MisterHW/EVAL-MP8862/doc/ev8862_image.jpg

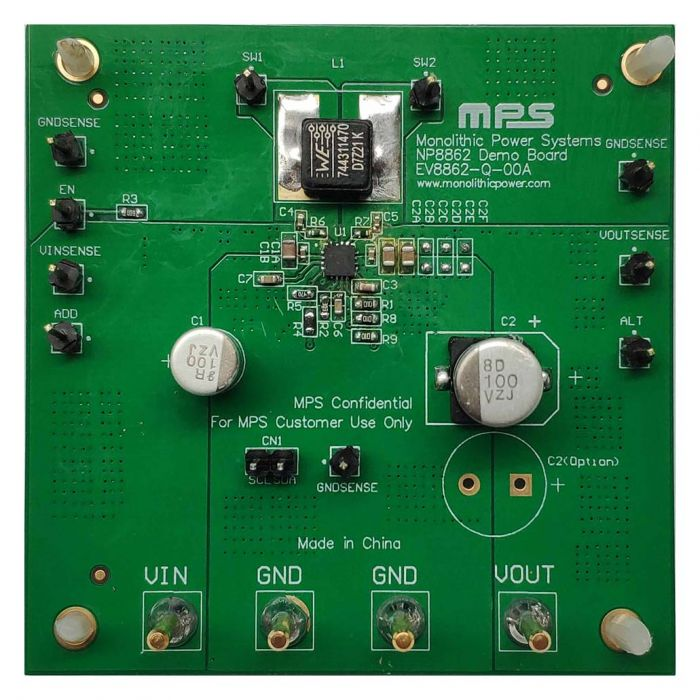
doc/ev8862_image.jpg
