MisterHW/EVAL-MP8862/img/read_0x00_0xFF_uart_starts_out_of_order_STM32F7_potential_problem.PNG

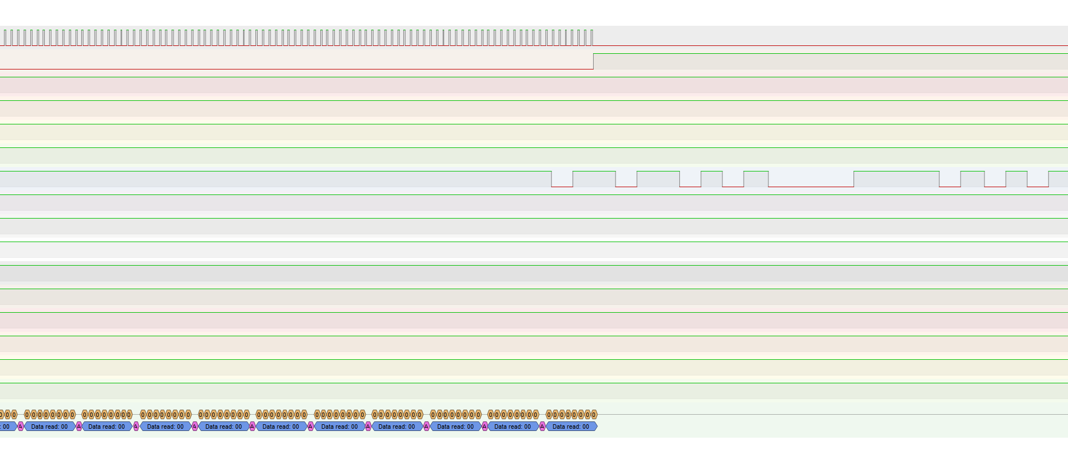
img/read_0x00_0xFF_uart_starts_out_of_order_STM32F7_potential_problem.PNG
