MisterHW/EVAL-MP8862/EVAL-MP8862-1A/gerber/EVAL-MP8862-In1_Cu.pdf

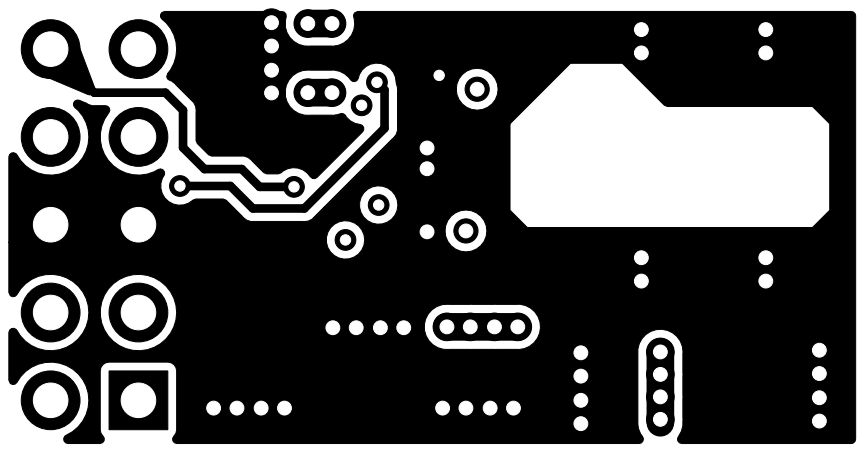
[picture p60: page 1]

File: EVAL-MP8862.kicad_pcb Sheet: https://github.com/MisterHW
