MisterHW/EVAL-MP8862/EVAL-MP8862-1A/gerber/EVAL-MP8862-In2_Cu.pdf

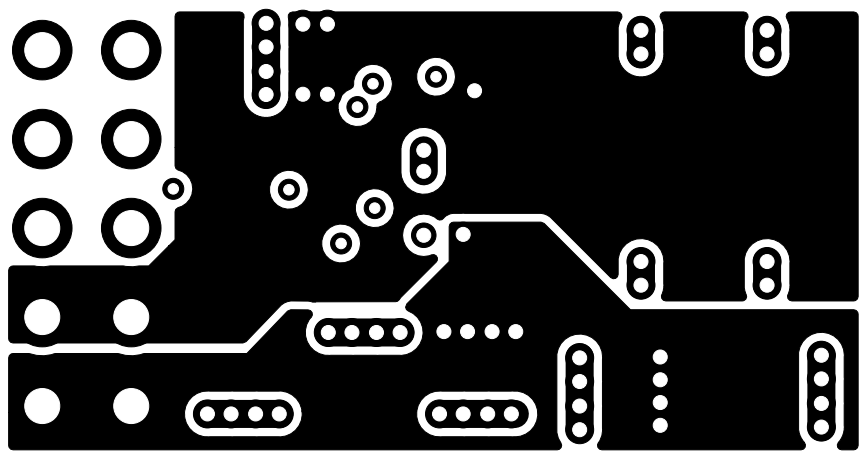
[picture p61: page 1]

File: EVAL-MP8862.kicad_pcb Sheet: https://github.com/MisterHW
