MisterHW/EVAL-MP8862/EVAL-MP8862-1B/gerber/EVAL-MP8862-B_Cu.pdf

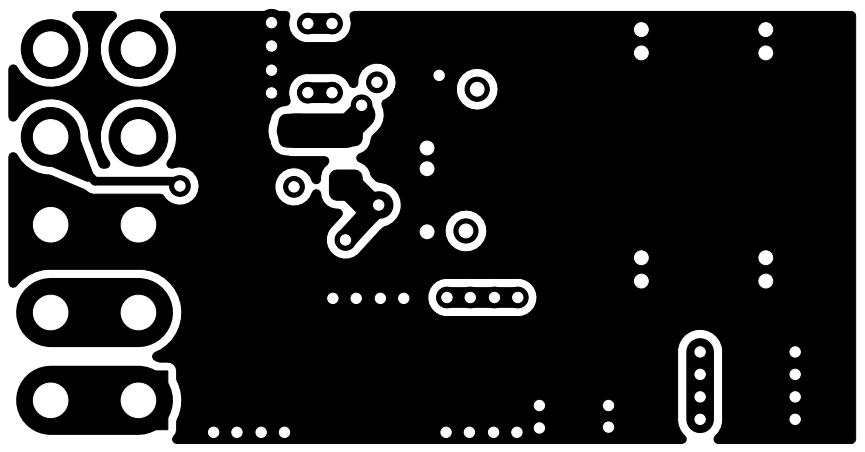
[picture p63: page 1]

File: EVAL-MP8862.kicad_pcb Sheet: https://github.com/MisterHW
