MisterHW/EVAL-MP8862/EVAL-MP8862-1B/gerber/EVAL-MP8862-B_Paste.pdf

File: EVAL-MP8862.kicad_pcb Sheet: https://github.com/MisterHW
