MisterHW/EVAL-MP8862/EVAL-MP8862-1B/gerber/EVAL-MP8862-F_Paste.pdf

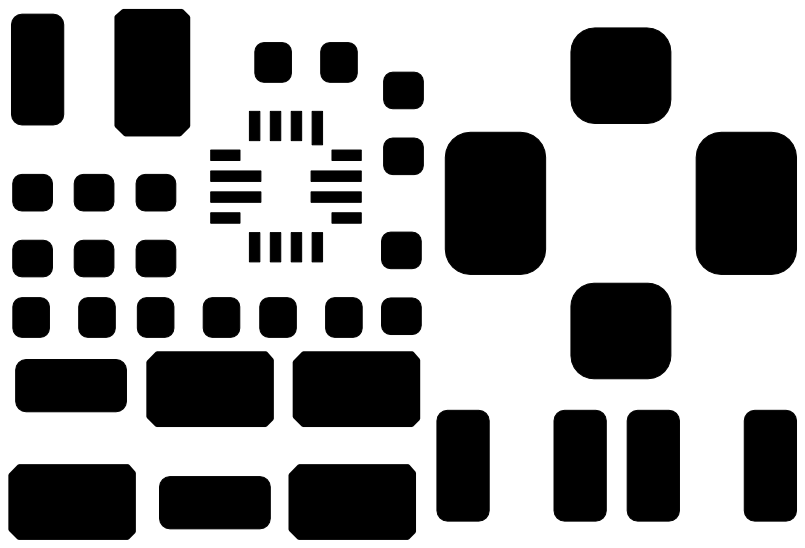
[picture p66: page 1]

File: EVAL-MP8862.kicad_pcb Sheet: https://github.com/MisterHW
