MisterHW/EVAL-MP8862/EVAL-MP8862-1B/gerber/EVAL-MP8862-In2_Cu.pdf

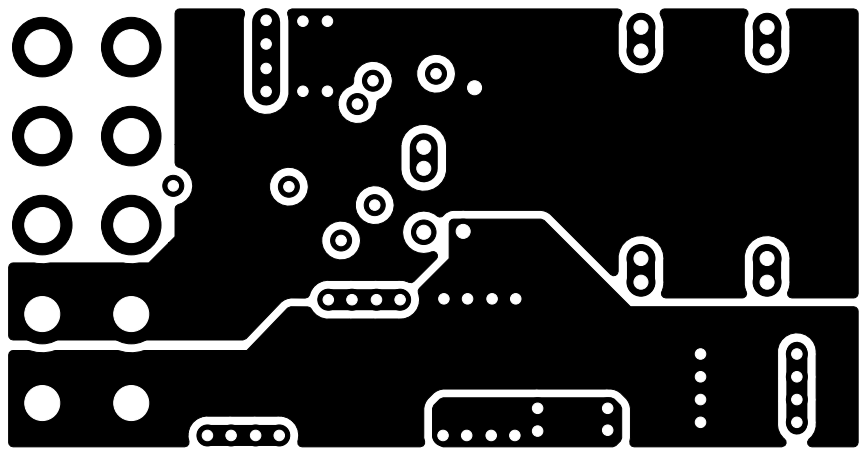
[picture p68: page 1]

File: EVAL-MP8862.kicad_pcb Sheet: https://github.com/MisterHW
