MisterHW/EVAL-MP8862/EVAL-MP8862-1B/gerber/EVAL-MP8862-B_Silkscreen.pdf

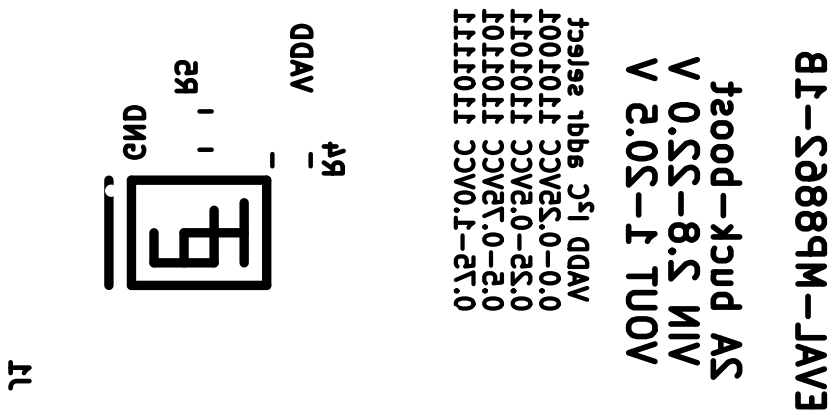
[picture p70: page 1]
