MisterHW/EVAL-MP8862/EVAL-MP8862-1B/gerber/EVAL-MP8862-F_Silkscreen.pdf

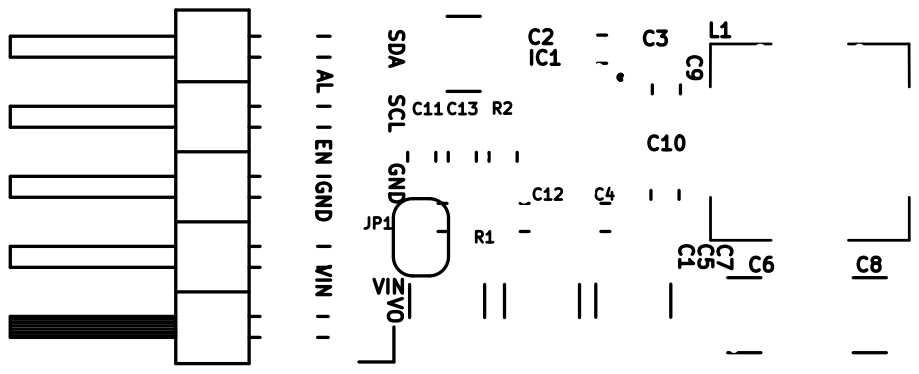
[picture p71: page 1]
